WB2CBA/ADX/ADX TOP view.jpg

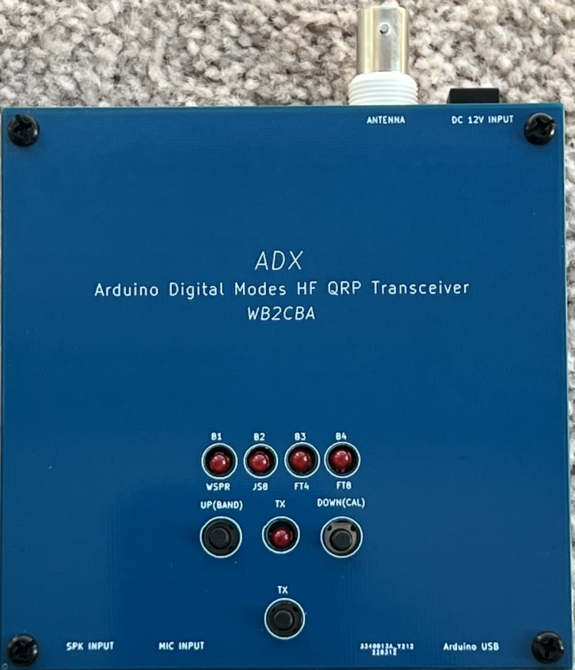
ADX TOP view.jpg
