WB2CBA/ADX/ADX Schematics and Layout/ADX component layout.jpg

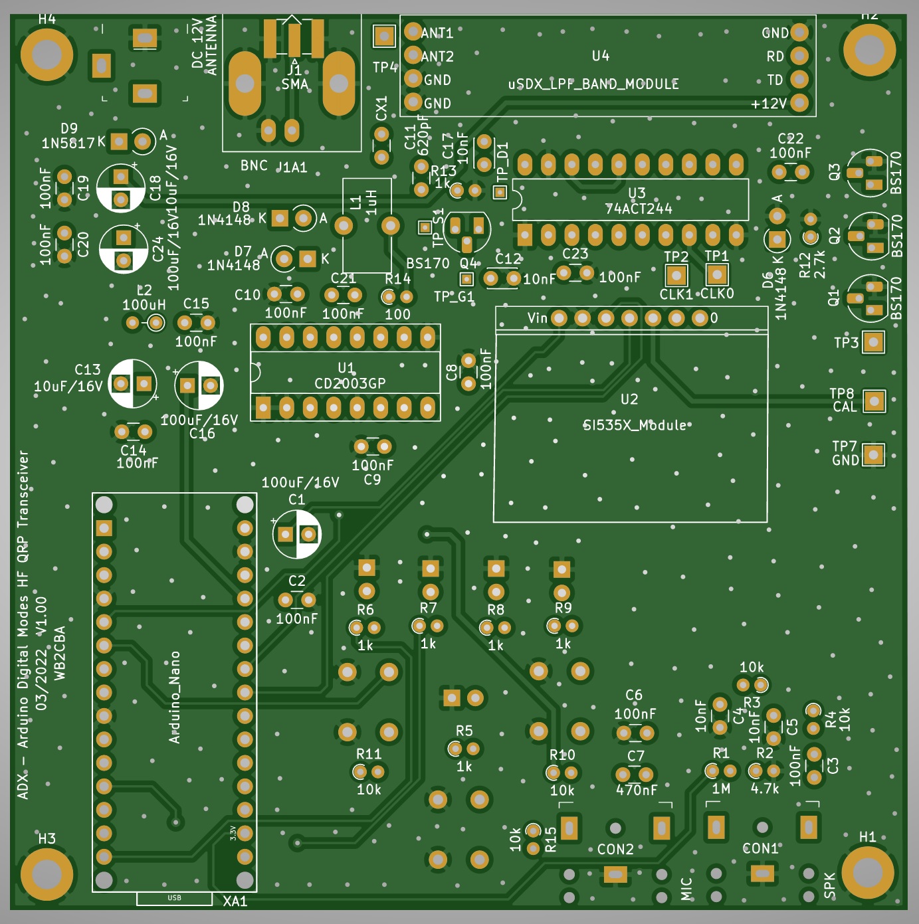
ADX Schematics and Layout/ADX component layout.jpg
